jantman/openscad-workbench-design/components/desktop_support.scad

module desktop_support()
{
    include <../config.scad>
    echo(str("BOM ITEM: desktop_support length=", table_depth, " material=", strut_timber_depth, "x", strut_timber_height));
    render() { // see note in README about rendering
        difference() {
            cube([strut_timber_depth,table_depth,strut_timber_height],false);

            // Rear cutout
            translate([0,table_depth-strut_timber_depth,0]){
                cube([strut_timber_depth,strut_timber_depth,strut_timber_height/2]);
            }
            // Front cutout
            cube([strut_timber_depth,strut_timber_depth,strut_timber_height/2]);
        }
    }
}
