jantman/openscad-workbench-design/components/lower_shelf.scad

module lower_shelf()
{
    include <../config.scad>
    echo(str("BOM ITEM: lower_shelf size=", table_width/4, "x", table_depth, " thickness=", shelf_thickness));
    render() { // see note in README about rendering
        difference() {
            cube([table_width/4,table_depth,shelf_thickness],false);

            // Left front cutout
            cube([leg_timber_width,leg_timber_depth,shelf_thickness]);
            // Right front cutout
            translate([(table_width/4)-leg_timber_width,0,0]){
              cube([leg_timber_width,leg_timber_depth,shelf_thickness]);
            }
            // Left rear cutout
            translate([0,table_depth-leg_timber_depth,0]){
              cube([leg_timber_width,leg_timber_depth,shelf_thickness]);
            }
            // Right rear cutout
            translate([(table_width/4)-leg_timber_width,table_depth-leg_timber_depth,0]){
              cube([leg_timber_width,leg_timber_depth,shelf_thickness]);
            }
            // Left center cutout
            translate([0,center_leg_setback-leg_timber_depth,0]){
              cube([center_leg_timber_width,center_leg_timber_depth,shelf_thickness]);
            }
            // Right center cutout
            translate([(table_width/4)-leg_timber_width,center_leg_setback-leg_timber_depth,0]){
              cube([center_leg_timber_width,center_leg_timber_depth,shelf_thickness]);
            }
        }
    }
}
