jantman/openscad-workbench-design/components/upper_side_tieA.scad

module upper_side_tieA()
{
    include <../config.scad>
    tie_length = (table_depth-center_leg_setback)+center_leg_timber_depth;
    render() { // see note in README about rendering
        if(top_shelf_timber_height >= top_shelf_timber_depth){
            difference() {
                echo(str("BOM ITEM: upper_side_tieA length=", tie_length, " material=", strut_timber_depth, "x", strut_timber_height));
                cube([strut_timber_depth,tie_length,strut_timber_height],false);

                // Left cutout
                translate([strut_timber_depth/2,tie_length-leg_timber_depth,0])
                {
                    cube([leg_timber_width/2,leg_timber_depth,strut_timber_height],false);
                }
                // Left bottom cutout
                translate([0,tie_length-(strut_timber_depth/2),0]){
                    cube([leg_timber_width/2,leg_timber_depth/2,strut_timber_height/2]);
                }
                // Right cutout
                translate([leg_timber_width/2,0,0])
                {
                    cube([leg_timber_width/2,leg_timber_depth,strut_timber_height],false);
                }
                // Right bottom cutout
                cube([leg_timber_width/2,strut_timber_depth/2,strut_timber_height/2]);
            }
        } else {
            difference() {
                echo(str("BOM ITEM: upper_side_tieA length=", tie_length, " material=", top_shelf_timber_depth, "x", top_shelf_timber_height));
                cube([top_shelf_timber_depth,tie_length,top_shelf_timber_height],false);
                // Left cutout
                translate([0,tie_length-leg_timber_depth,0])
                {
                    cube([top_shelf_timber_depth,top_shelf_timber_depth,top_shelf_timber_height/2],false);
                }
                // Right cutout
                translate([0,0,0])
                {
                    cube([top_shelf_timber_depth,top_shelf_timber_depth,top_shelf_timber_height/2],false);
                }
            }
        }
    }
}
