jantman/openscad-workbench-design/shelf_support_3d_print/shelf_support.scad

use <../components/shelf_support.scad>

scale([25.4,25.4,25.4]){ // inches to mm
    shelf_support();
}
